netmana808/catbadge/work/v8_7/preview/button_detail.png

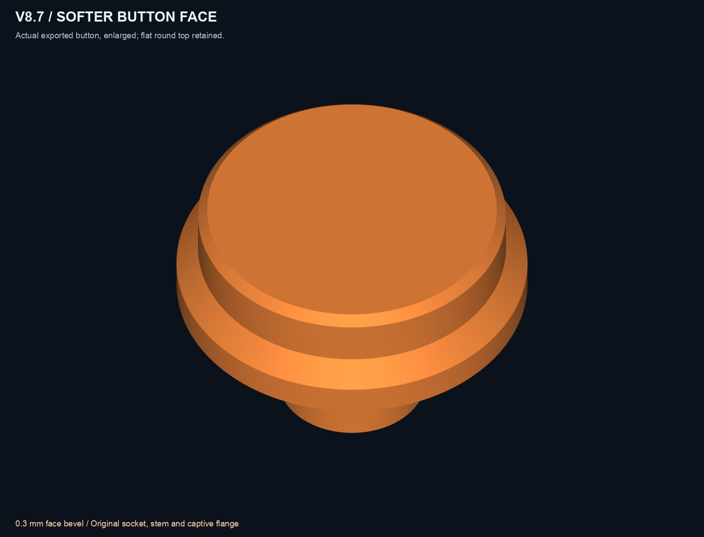
work/v8_7/preview/button_detail.png
