netmana808/catbadge/work/v8_7/preview/closed_ears.png

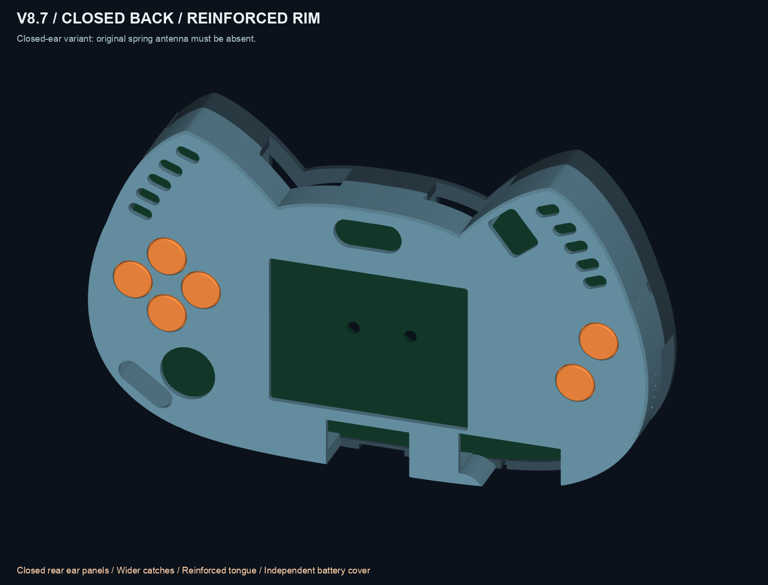
work/v8_7/preview/closed_ears.png
