netmana808/catbadge/work/v8_7/preview/grip_detail.png

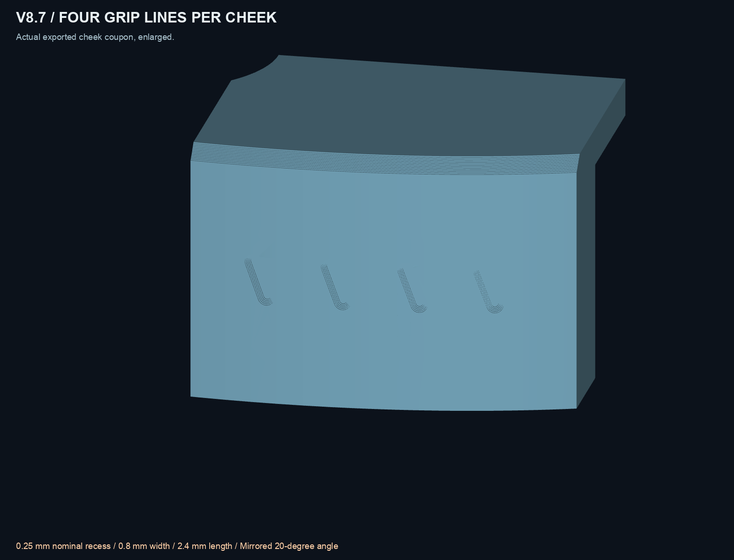
work/v8_7/preview/grip_detail.png
