netmana808/catbadge/work/v8_7/preview/latch.png

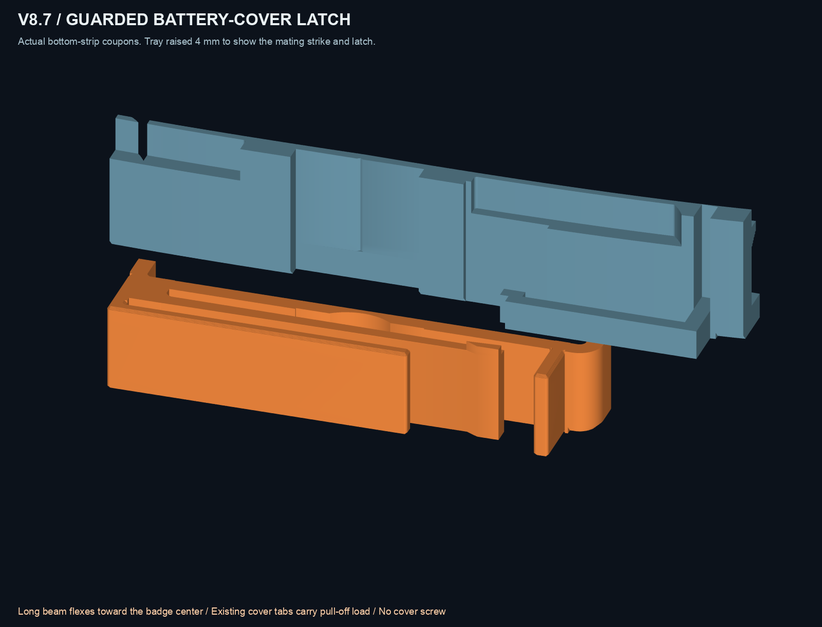
work/v8_7/preview/latch.png
