netmana808/catbadge/work/v8_7/preview/rim_inside.png

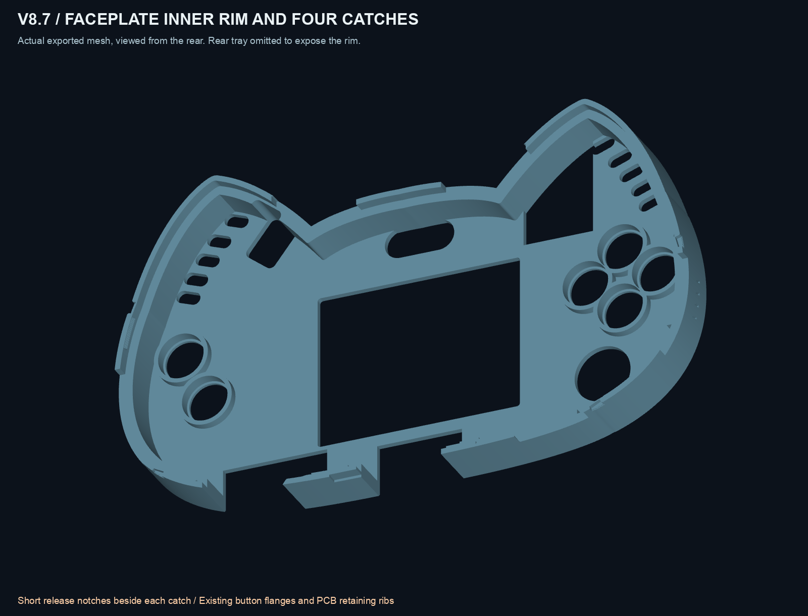
work/v8_7/preview/rim_inside.png
