netmana808/catbadge/work/v8_7b/preview/comparison-raw.png

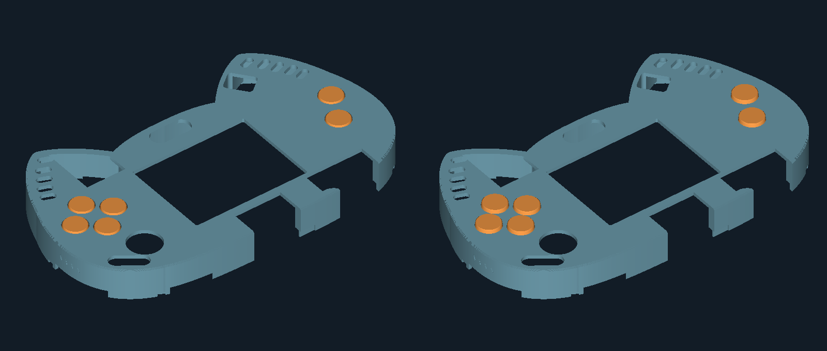
work/v8_7b/preview/comparison-raw.png
