netmana808/catbadge/work/v8_7b/preview/fit-trial-layout.png

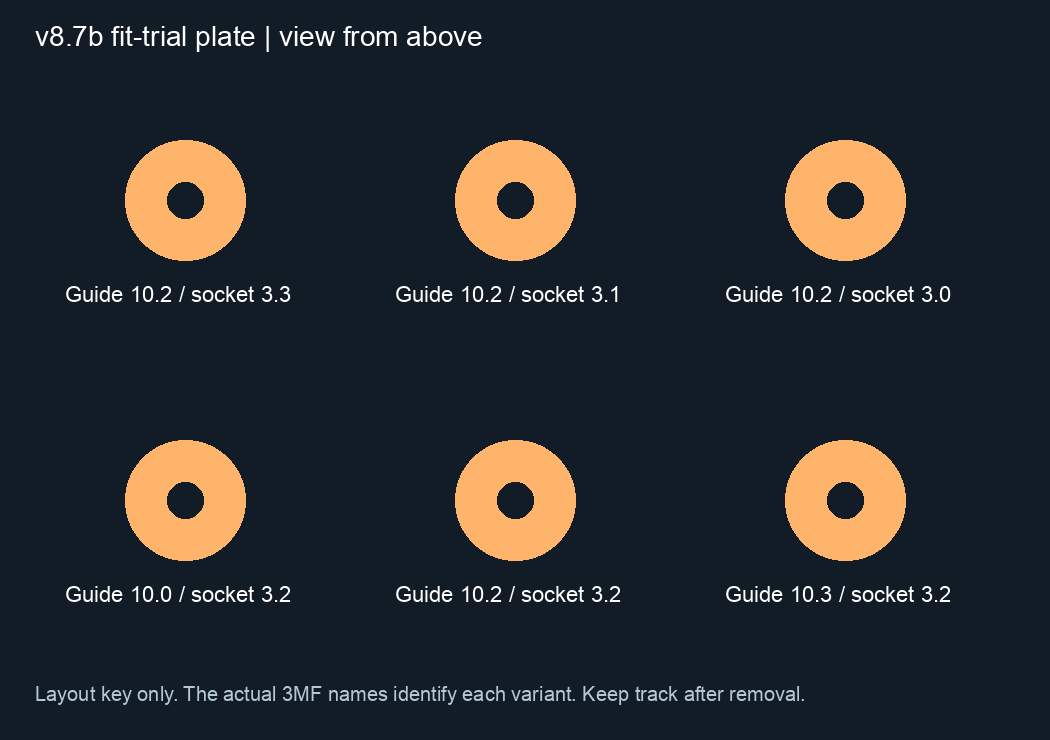
work/v8_7b/preview/fit-trial-layout.png
