netmana808/catbadge/work/v8_7/preview/PRINT_FIRST_front_buttons_ASSEMBLY.stl

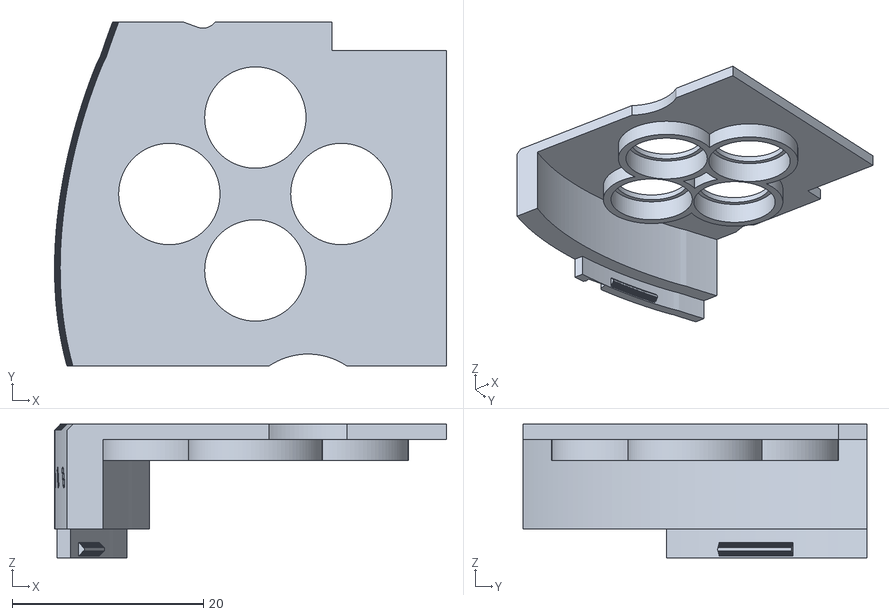
[picture p27: CAD file, 2026-09-10]
work/v8_7/preview/PRINT_FIRST_front_buttons_ASSEMBLY.stl
41.0 x 36.0 x 14.0
