netmana808/catbadge/work/v8_7/preview/PRINT_FIRST_rim_tray_ASSEMBLY.stl

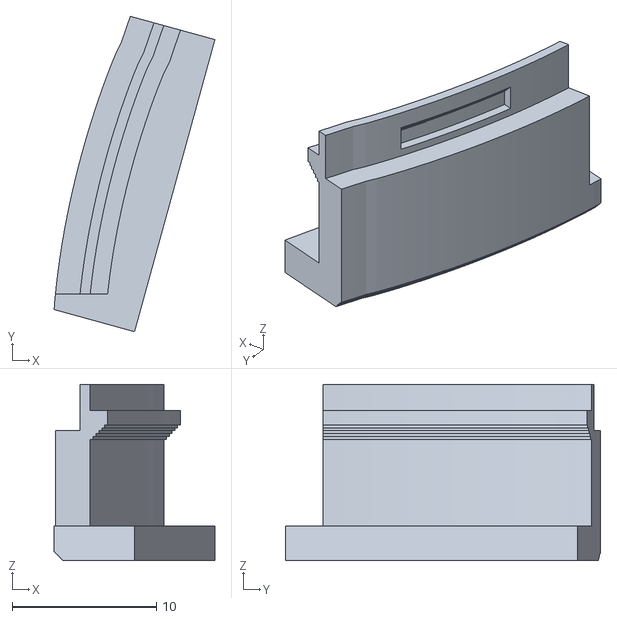
[picture p28: CAD file, 2026-09-10]
work/v8_7/preview/PRINT_FIRST_rim_tray_ASSEMBLY.stl
11.2 x 21.9 x 12.2
