netmana808/catbadge/work/v8_7/preview/PRINT_FIRST_closed_rear_ear_ASSEMBLY.stl

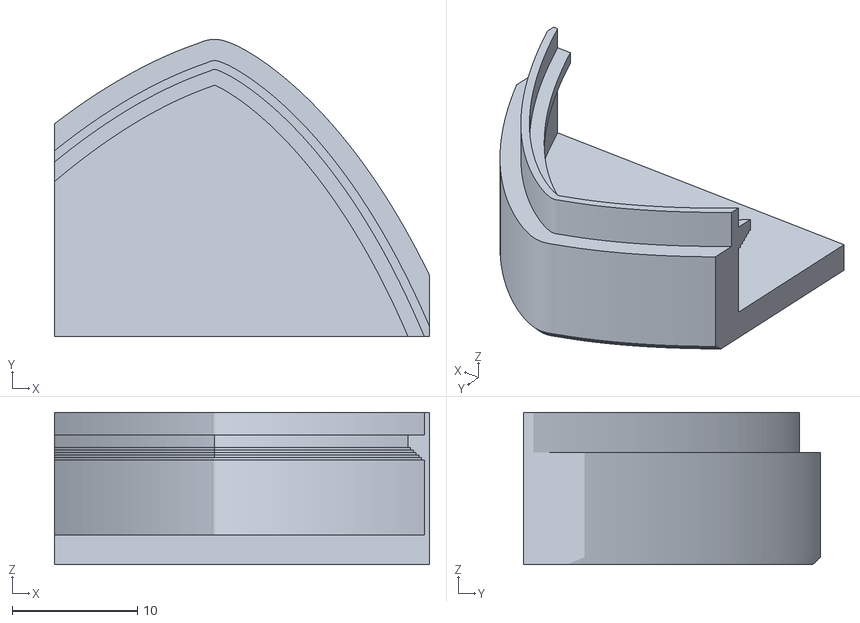
[picture p29: CAD file, 2026-09-10]
work/v8_7/preview/PRINT_FIRST_closed_rear_ear_ASSEMBLY.stl
30.0 x 23.8 x 12.2
