netmana808/catbadge/work/v8_7/preview/PRINT_FIRST_cover_edge_ASSEMBLY.stl

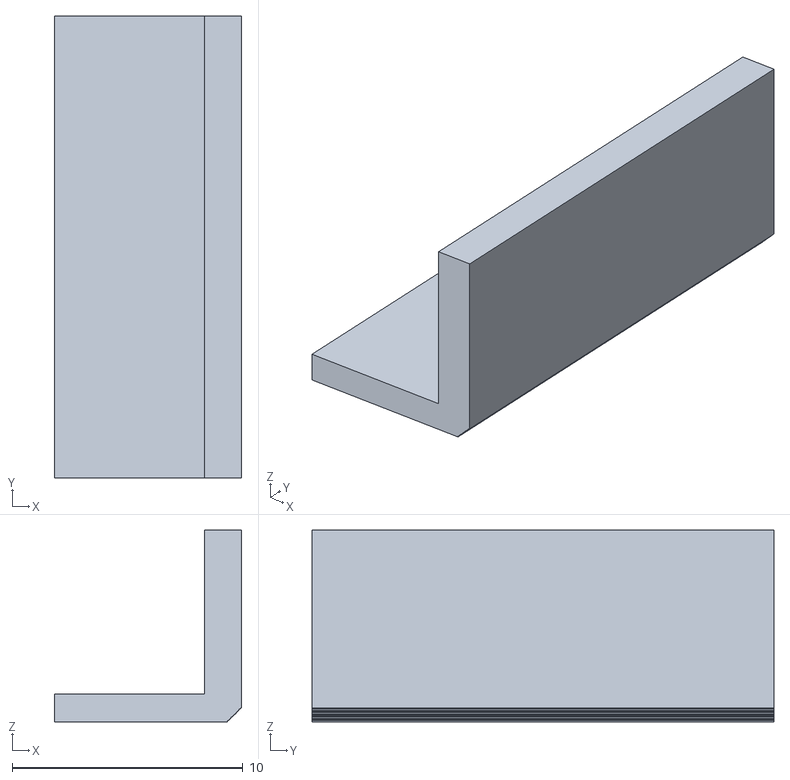
[picture p30: CAD file, 2026-09-10]
work/v8_7/preview/PRINT_FIRST_cover_edge_ASSEMBLY.stl
8.10 x 20.0 x 8.30
