netmana808/catbadge/work/v8_7/preview/PRINT_FIRST_screen_52p5x40_ASSEMBLY.stl

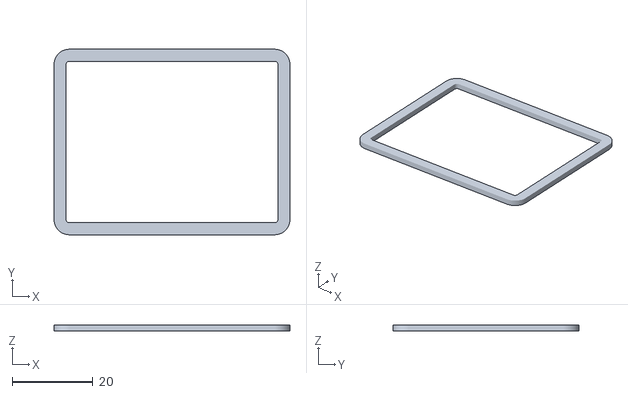
[picture p31: CAD file, 2026-09-09]
work/v8_7/preview/PRINT_FIRST_screen_52p5x40_ASSEMBLY.stl
58.5 x 46.0 x 1.60
