netmana808/catbadge/work/v8_7/preview/PRINT_FIRST_cheek_grip_ASSEMBLY.stl

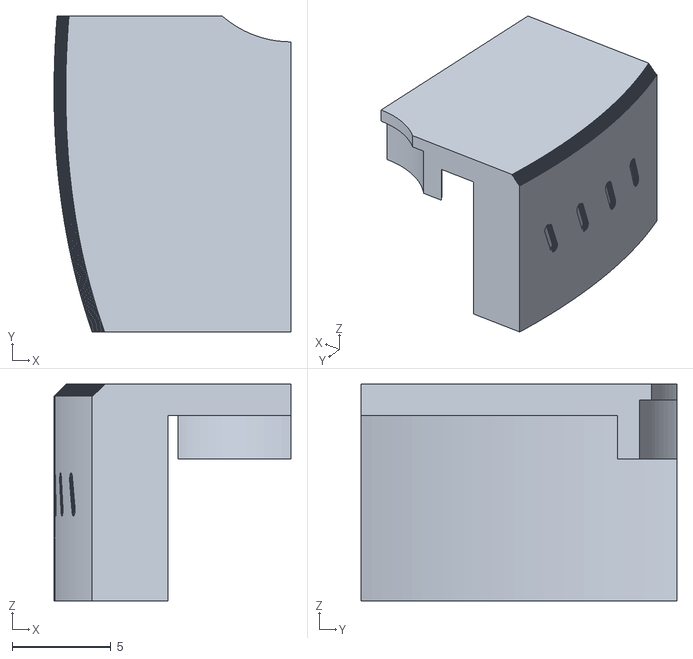
[picture p32: CAD file, 2026-09-09]
work/v8_7/preview/PRINT_FIRST_cheek_grip_ASSEMBLY.stl
12.0 x 16.0 x 11.0
