netmana808/catbadge/work/v8_7/preview/pcb_REFERENCE_ASSEMBLY.stl

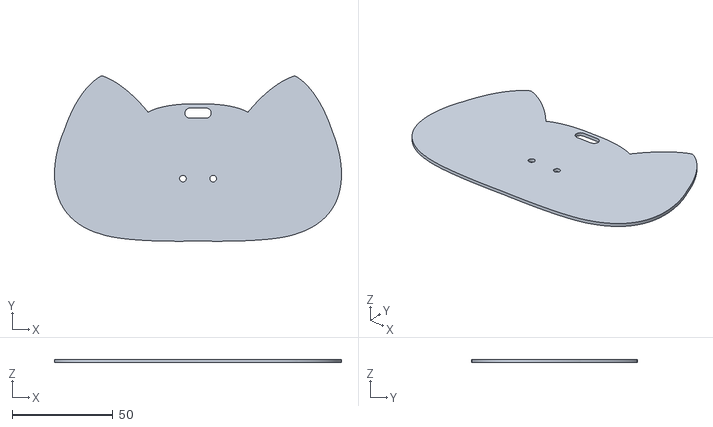
[picture p33: CAD file, 2026-09-09]
work/v8_7/preview/pcb_REFERENCE_ASSEMBLY.stl
142.4 x 82.1 x 1.60
