netmana808/catbadge/work/v8_7/CatBadge-v8.7-COMBINED-CLOSED-BACK.3mf

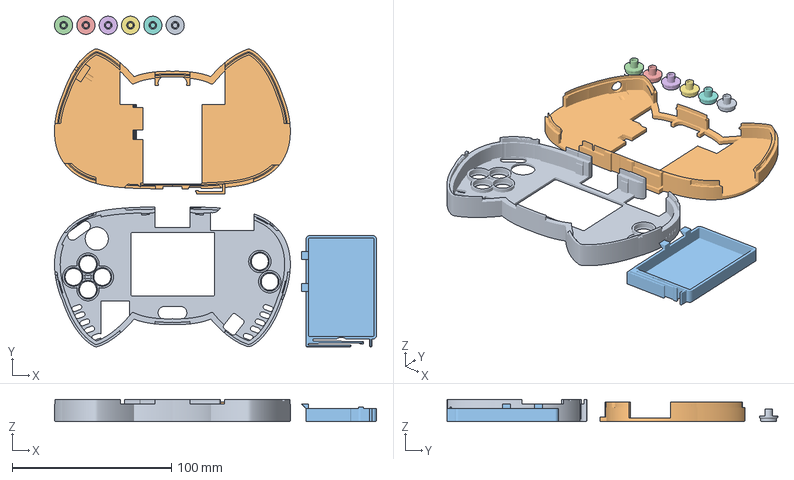
[picture p34: CAD file, 2026-09-10]
work/v8_7/CatBadge-v8.7-COMBINED-CLOSED-BACK.3mf
202.0 x 207.4 x 14.0 mm
faceplate
rear_tray
battery_cover
button_LEFT_TRIAL_3p2
button_UP_TRIAL_3p2
button_DOWN_TRIAL_3p2
button_RIGHT_TRIAL_3p2
button_B_TRIAL_3p2
button_A_TRIAL_3p2
