netmana808/catbadge/work/v8_7a/parts/CatBadge-v8.7a-Rear-Tray-Adhesion-Tabs.3mf

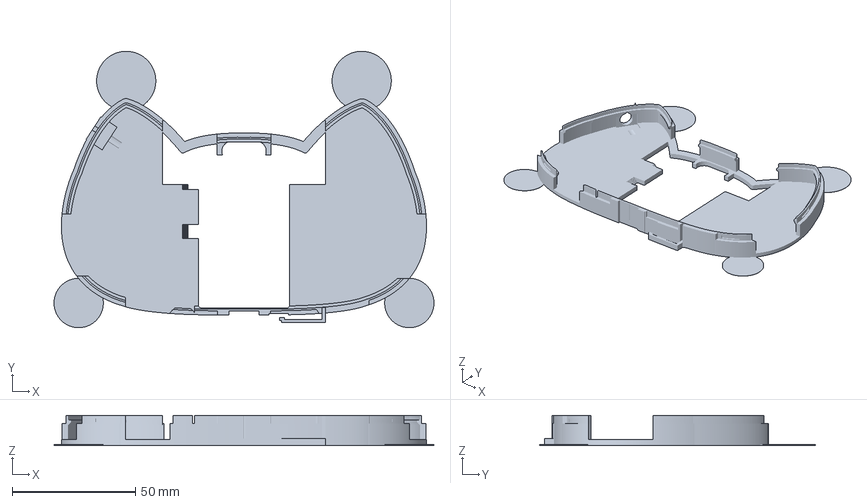
[picture p35: CAD file, 2026-09-10]
work/v8_7a/parts/CatBadge-v8.7a-Rear-Tray-Adhesion-Tabs.3mf
154.0 x 112.0 x 12.2 mm
