netmana808/catbadge/work/v8_7a/tests/PRINT_FIRST_v8.7a_Ear_Pad_Removal.3mf

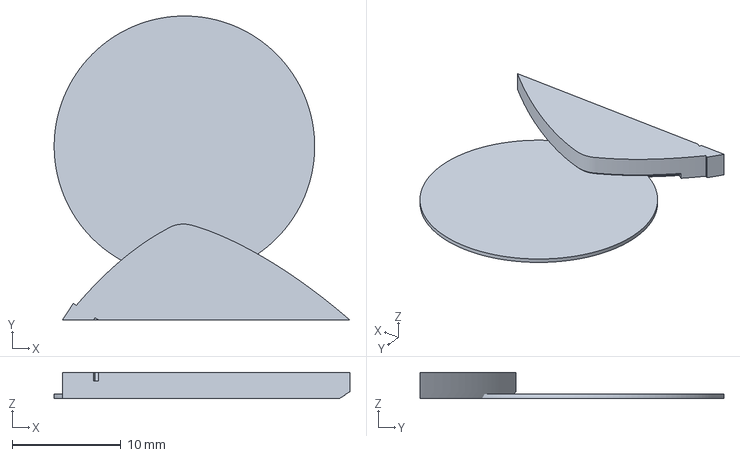
[picture p36: CAD file, 2026-09-10]
work/v8_7a/tests/PRINT_FIRST_v8.7a_Ear_Pad_Removal.3mf
27.2 x 28.0 x 2.40 mm
