netmana808/catbadge/work/v8_7b/PRINT_FIRST_v8.7b_Button_Fit_Trials.3mf

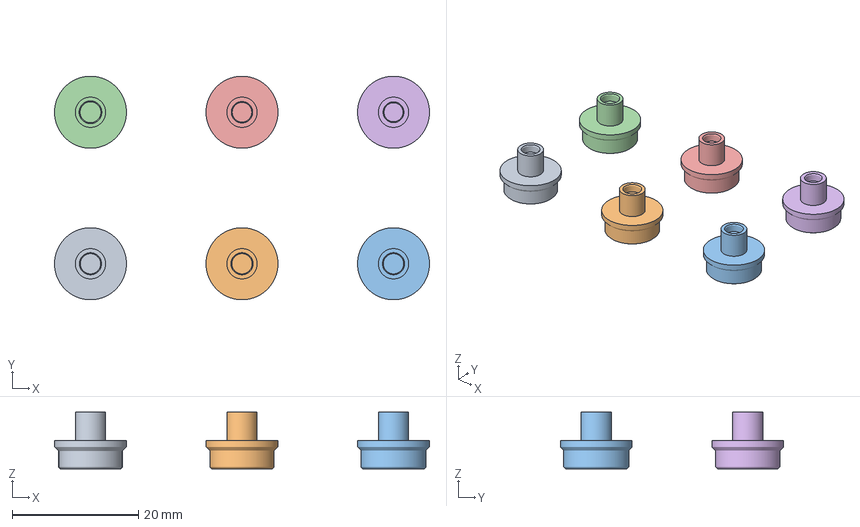
[picture p37: CAD file, 2026-09-10]
work/v8_7b/PRINT_FIRST_v8.7b_Button_Fit_Trials.3mf
59.4 x 35.4 x 9.00 mm
cap_G10p0_S3p2_PLUS1mm
cap_G10p2_S3p2_PLUS1mm
cap_G10p3_S3p2_PLUS1mm
cap_G10p2_S3p3_PLUS1mm
cap_G10p2_S3p1_PLUS1mm
cap_G10p2_S3p0_PLUS1mm
