netmana808/catbadge/work/v8_7/PRINT_FIRST_v8.7_Snap_Only.3mf

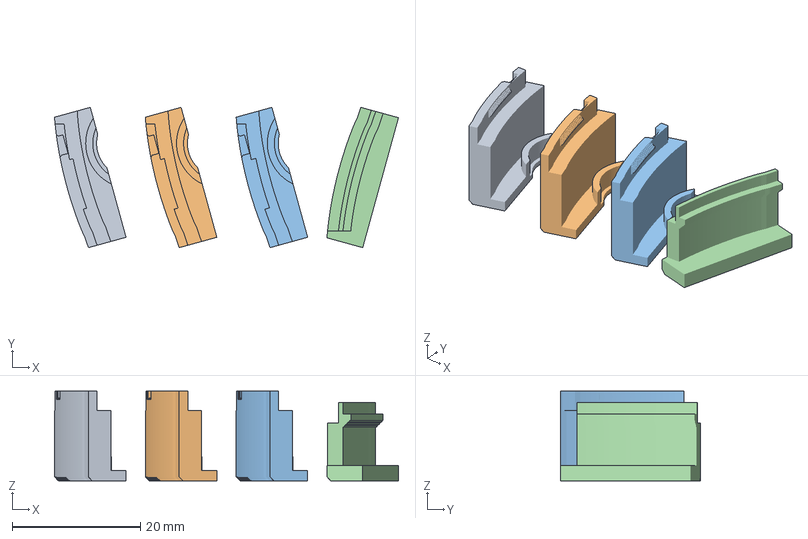
[picture p39: CAD file, 2026-09-10]
work/v8_7/PRINT_FIRST_v8.7_Snap_Only.3mf
53.6 x 21.9 x 14.0 mm
PRINT_FIRST_rim_lid_0p25
PRINT_FIRST_rim_lid_0p35
PRINT_FIRST_rim_lid_0p45
PRINT_FIRST_rim_tray
