netmana808/catbadge/work/v8_7/PRINT_FIRST_v8.7_Fit_and_Comfort.3mf

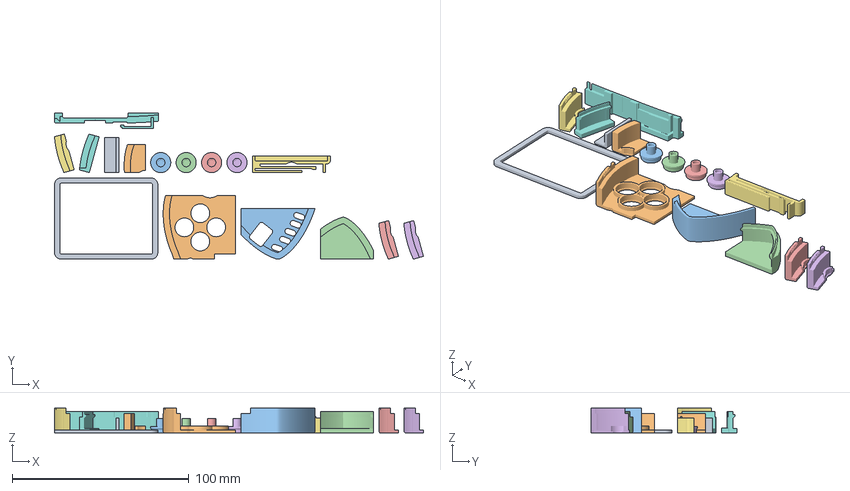
[picture p40: CAD file, 2026-09-10]
work/v8_7/PRINT_FIRST_v8.7_Fit_and_Comfort.3mf
208.9 x 82.9 x 14.0 mm
PRINT_FIRST_screen_52p5x40
PRINT_FIRST_front_buttons
PRINT_FIRST_right_ear_SAO
PRINT_FIRST_closed_rear_ear
PRINT_FIRST_rim_lid_0p25
PRINT_FIRST_rim_lid_0p35
PRINT_FIRST_rim_lid_0p45
PRINT_FIRST_rim_tray
PRINT_FIRST_cover_edge
PRINT_FIRST_cheek_grip
cap_socket_3p0
cap_socket_3p1
cap_socket_3p2
cap_socket_3p3
PRINT_FIRST_latch_cover
PRINT_FIRST_latch_tray
