netmana808/catbadge/work/v8_7/PRINT_FIRST_v8.7_Comfort_Only.3mf

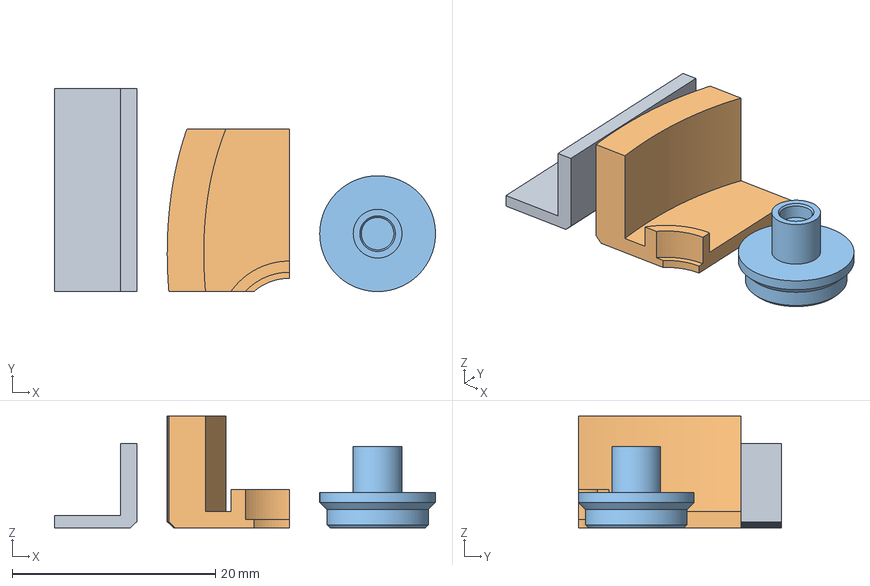
[picture p41: CAD file, 2026-09-10]
work/v8_7/PRINT_FIRST_v8.7_Comfort_Only.3mf
37.5 x 20.0 x 11.0 mm
PRINT_FIRST_cover_edge
PRINT_FIRST_cheek_grip
cap_socket_3p2
